Djayden-R/Heating-Panel-Customisation/Circuit/Device wiring.kicad_sch

## KiCad design Circuit/Device wiring.kicad_sch (2025-12-27)

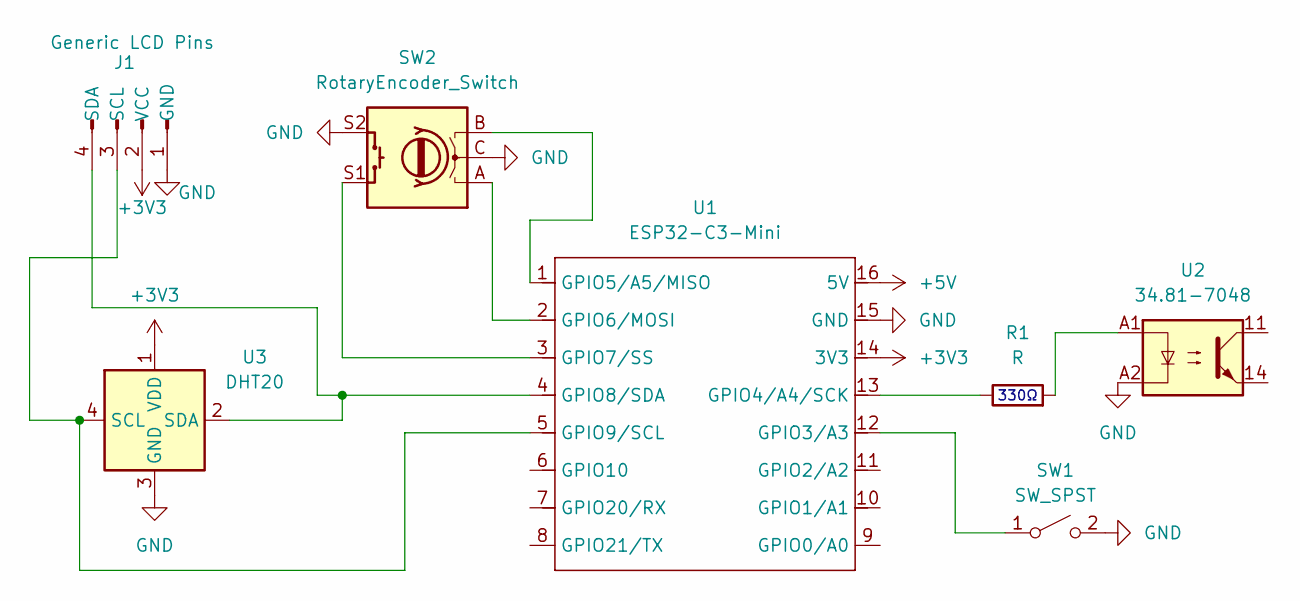
[picture p19: schematic Device wiring.kicad_sch]

Parts:
J1: Generic LCD Pins
R1: R
SW1: SW_SPST
SW2: RotaryEncoder_Switch
U1: ESP32-C3-Mini
U2: 34.81-7048; Finder_34.81
U3: DHT20; Aosong_DHT11_5.5x12.0_P2.54mm

Connections:
+3V3: J1.2 (VCC), U1.14 (3V3), U3.1 (VDD)
+5V: U1.16 (5V)
GND: J1.1 (GND), SW1.2 (B), SW2.C, SW2.S2, U1.15 (GND), U2.A2, U3.3 (GND)
unnamed: J1.3 (SCL), U1.5 (GPIO9/SCL), U3.4 (SCL)
unnamed: J1.4 (SDA), U1.4 (GPIO8/SDA), U3.2 (SDA)
unnamed: R1.1, U1.13 (GPIO4/A4/SCK)
unnamed: R1.2, U2.A1
unnamed: SW1.1 (A), U1.12 (GPIO3/A3)
unnamed: SW2.A, U1.2 (GPIO6/MOSI)
unnamed: SW2.B, U1.1 (GPIO5/A5/MISO)
unnamed: SW2.S1, U1.3 (GPIO7/SS)

Notes on the sheet:
330Ω
